sergey12malyshev/RF_HACK/application/workStates.c

#include <stdbool.h>

#include "workStates.h"

static Work_state_t mainState;

void setWorkState(const Work_state_t s)
{
  mainState = s;
}

Work_state_t getWorkState(void)
{
  return mainState;
}

bool isWorkStateSet(Work_state_t s)
{
  return (bool) (s == mainState);
}
