sergey12malyshev/RF_HACK/Core/Src/adc.c

/**
  ******************************************************************************
  * @file    adc.c
  * @brief   This file provides code for the configuration
  *          of the ADC instances.
  ******************************************************************************
  * @attention
  *
  * <h2><center>&copy; Copyright (c) 2024 STMicroelectronics.
  * All rights reserved.</center></h2>
  *
  * This software component is licensed by ST under BSD 3-Clause license,
  * the "License"; You may not use this file except in compliance with the
  * License. You may obtain a copy of the License at:
  *                        opensource.org/licenses/BSD-3-Clause
  *
  ******************************************************************************
  */

/* Includes ------------------------------------------------------------------*/
#include "adc.h"

/* USER CODE BEGIN 0 */

typedef struct _Adc
{
  uint16_t adc;
  uint32_t voltage;
  uint32_t voltage_average;
}Adc;

static Adc vdda = {0};

uint16_t getAdcVDDA(void)
{
  return vdda.adc;
}

uint32_t getVoltageVDDA(void)
{
  return vdda.voltage;
}

uint32_t getVoltageVDDA_Av(void)
{
  return vdda.voltage_average;
}

char generateRandomChar(void)
{
  return (char)(getAdcVDDA() & 127);
}

void adc_enable(void)
{
  __IO uint32_t wait_loop_index = 0;

  LL_ADC_Enable(ADC1);

  wait_loop_index = ((LL_ADC_DELAY_TEMPSENSOR_STAB_US * (SystemCoreClock / (100000 * 2))) / 10); //!!!
  while(wait_loop_index != 0)
  {
    wait_loop_index--;
  }
  // ADC calibration is not required for the stm32F4 series
}

static uint16_t adc_convertData(void)
{
  LL_ADC_REG_StartConversionSWStart(ADC1);
  while (!LL_ADC_IsActiveFlag_EOCS(ADC1)) {}
  LL_ADC_ClearFlag_EOCS(ADC1);

  return LL_ADC_REG_ReadConversionData12(ADC1);
}

static uint32_t adc_convertVDDA(uint16_t adcData)
{
  return (((uint32_t) *VREFINT_CAL_ADDR) * (uint32_t)3300) / adcData;
}

/* 
* Exponential running average  filt = (A * filt + signal) >> k, https://alexgyver.ru/lessons/filters/ 
*/
static uint32_t filt = 0;

uint16_t expRunningAverageFilter(uint16_t input)
{
  const uint8_t k = 2;
  const uint8_t a = 3; // a =  (2^k) – 1

  filt = (a * filt + input) >> k;

  return filt;
}

/*
* Preset the filter to speed up getting the correct value
*/
void setDefaultValueFilter(uint16_t defValue)
{
  filt = defValue;
}

void adcConvertProcess(void)
{
  vdda.adc = adc_convertData();
  vdda.voltage = adc_convertVDDA(vdda.adc);
  vdda.voltage_average = expRunningAverageFilter(vdda.voltage);
}


/* USER CODE END 0 */

/* ADC1 init function */
void MX_ADC1_Init(void)
{

  LL_ADC_InitTypeDef ADC_InitStruct = {0};
  LL_ADC_REG_InitTypeDef ADC_REG_InitStruct = {0};
  LL_ADC_CommonInitTypeDef ADC_CommonInitStruct = {0};

  /* Peripheral clock enable */
  LL_APB2_GRP1_EnableClock(LL_APB2_GRP1_PERIPH_ADC1);

  /** Common config
  */
  ADC_InitStruct.Resolution = LL_ADC_RESOLUTION_12B;
  ADC_InitStruct.DataAlignment = LL_ADC_DATA_ALIGN_RIGHT;
  ADC_InitStruct.SequencersScanMode = LL_ADC_SEQ_SCAN_DISABLE;
  LL_ADC_Init(ADC1, &ADC_InitStruct);
  ADC_REG_InitStruct.TriggerSource = LL_ADC_REG_TRIG_SOFTWARE;
  ADC_REG_InitStruct.SequencerLength = LL_ADC_REG_SEQ_SCAN_DISABLE;
  ADC_REG_InitStruct.SequencerDiscont = LL_ADC_REG_SEQ_DISCONT_DISABLE;
  ADC_REG_InitStruct.ContinuousMode = LL_ADC_REG_CONV_SINGLE;
  ADC_REG_InitStruct.DMATransfer = LL_ADC_REG_DMA_TRANSFER_NONE;
  LL_ADC_REG_Init(ADC1, &ADC_REG_InitStruct);
  LL_ADC_REG_SetFlagEndOfConversion(ADC1, LL_ADC_REG_FLAG_EOC_UNITARY_CONV);
  ADC_CommonInitStruct.CommonClock = LL_ADC_CLOCK_SYNC_PCLK_DIV4;
  LL_ADC_CommonInit(__LL_ADC_COMMON_INSTANCE(ADC1), &ADC_CommonInitStruct);
  /** Configure Regular Channel
  */
  LL_ADC_REG_SetSequencerRanks(ADC1, LL_ADC_REG_RANK_1, LL_ADC_CHANNEL_VREFINT);
  LL_ADC_SetChannelSamplingTime(ADC1, LL_ADC_CHANNEL_VREFINT, LL_ADC_SAMPLINGTIME_3CYCLES);
  LL_ADC_SetCommonPathInternalCh(__LL_ADC_COMMON_INSTANCE(ADC1), LL_ADC_PATH_INTERNAL_VREFINT);
}

/************************ (C) COPYRIGHT STMicroelectronics *****END OF FILE****/
