sergey12malyshev/RF_HACK/application/cli_Thread.h

#pragma once
#ifndef __CLI_TASK_H__
#define __CLI_TASK_H__

#define LC_INCLUDE "lc-addrlabels.h"
#include "pt.h"

PT_THREAD(CLI_Thread(struct pt *pt));

void cli_init(void);
void cli_uart_callBack(void);

#endif /*__CLI_TASK_H__ */
