sergey12malyshev/RF_HACK/application/configFile.h

#pragma once

#ifndef _CONFIG_H_
#define _CONFIG_H_

#include <stdbool.h>

#define CALIBRATE_EN              false       // Activating touchscreen calibration

#define RUN_LCD_DEMO              false       // Enabling demo mode for the display

#define CC1101_CUSTOM_OLD_CONFIG  false       // Enabling old CC1101 initialization

#define TX_MODE_ALWAYS            false       // Enabling continuous transmission mode

#define CLI_ENABLE                true        // Enabling the command line

#endif // _CONFIG_H_
