sergey12malyshev/RF_HACK/application/subGHz_TX_Thread.c

#include <stdbool.h>
#include <stdlib.h>
#include <stdio.h>
#include <string.h>

#define LC_INCLUDE "lc-addrlabels.h"
#include "pt.h"

#include "main.h"
#include "subGHz_TX_Thread.h"
#include "application_Thread.h"
#include "cli_driver.h"
#include "cc1101.h"
#include "time.h"

#include "display.h"
#include "displayInit.h"
#include "ili9341.h"


static char packet[7] = "QWERTY";; // Reserve one character for a null terminator!

/*
 * Protothread subGHz_TX_Thread
 *
 *
 */
PT_THREAD(subGHz_TX_Thread(struct pt *pt))
{
  static uint32_t timer1;
  
  PT_BEGIN(pt);

  PT_DELAY_MS(pt, &timer1, 250);
  
  screen_clear();
  LCD_WriteString(lcd, 0, 0, "TX mode", &Font_8x13, COLOR_RED, COLOR_BLACK, LCD_SYMBOL_PRINT_FAST);

  CC1101_reinit();

  setTime(&timer1);


  while (1)
  {       
    PT_WAIT_UNTIL(pt, timer(&timer1, 350));

    static uint8_t count_tx = 0;

    if (count_tx >= 99)
    {
      count_tx = 0;
    }
    sprintf(packet, "TST %02d", count_tx++);

    uint8_t result = CC1101_transmitt_packet(packet, sizeof(packet)); // the function is sending the data

    if (result > 0)
    {
      DEBUG_PRINT("TX ERROR: %d"CLI_NEW_LINE, result);
    }

    LCD_WriteString(lcd, 15, 40, packet, &Font_12x20, COLOR_RED, COLOR_BLACK, LCD_SYMBOL_PRINT_FAST);

    static uint32_t tx_timeout;
    tx_timeout = HAL_GetTick() + 100;

    PT_WAIT_UNTIL(pt, (CC1101_GDO0_flag_get() || (HAL_GetTick() > tx_timeout))); // (low lowel - end transmitt)
    if (!CC1101_GDO0_flag_get())
    {
      DEBUG_PRINT("TX TIMEOUT"CLI_NEW_LINE);
    }
    CC1101_GDO0_flag_clear();

    PT_YIELD(pt);
  }

  PT_END(pt);
}
