sergey12malyshev/RF_HACK/application/frequencyChannelsTable.c

#include "frequencyChannelsTable.h"

const float freqLpdList[69] = 
{
  LPD1, LPD2, LPD3, LPD4, LPD5, LPD6, LPD7, LPD8, LPD9, LPD10, LPD11, LPD12, LPD13, LPD14, LPD15, LPD16, LPD17, LPD18, LPD19,
  LPD20, LPD21, LPD22, LPD23, LPD24, LPD25, LPD26, LPD27, LPD28, LPD29, LPD30, LPD31, LPD32, LPD33, LPD34, LPD35, LPD36, LPD37, 
  LPD38, LPD39, LPD40, LPD41, LPD42, LPD43, LPD44, LPD45, LPD46, LPD47, LPD48, LPD49, LPD50, LPD51, LPD52, LPD53, LPD54, LPD55, 
  LPD56, LPD57, LPD58, LPD59, LPD60, LPD61, LPD62, LPD63, LPD64, LPD65, LPD66, LPD67, LPD68, LPD69
};
