sergey12malyshev/RF_HACK/application/frequencyChannelsTable.h

#pragma once

#define LPD1    433.075
#define LPD2    433.100
#define LPD3    433.125
#define LPD4    433.150
#define LPD5    433.175
#define LPD6    433.200
#define LPD7    433.225
#define LPD8    433.250
#define LPD9    433.275
#define LPD10   433.300
#define LPD11   433.325
#define LPD12   433.350
#define LPD13   433.375
#define LPD14   433.400
#define LPD15   433.425
#define LPD16   433.450
#define LPD17   433.475
#define LPD18   433.500
#define LPD19   433.525
#define LPD20   433.550
#define LPD21   433.575
#define LPD22   433.600
#define LPD23   433.625
#define LPD24   433.650
#define LPD25   433.675
#define LPD26   433.700
#define LPD27   433.725
#define LPD28   433.750
#define LPD29   433.775
#define LPD30   433.800
#define LPD31   433.825
#define LPD32   433.850
#define LPD33   433.875
#define LPD34   433.900
#define LPD35   433.925
#define LPD36   433.950
#define LPD37   433.975
#define LPD38   434.000
#define LPD39   434.025
#define LPD40   434.050
#define LPD41   434.075
#define LPD42   434.100
#define LPD43   434.125
#define LPD44   434.150
#define LPD45   434.175
#define LPD46   434.200
#define LPD47   434.225
#define LPD48   434.250
#define LPD49   434.275
#define LPD50   434.300
#define LPD51   434.325
#define LPD52   434.350
#define LPD53   434.375
#define LPD54   434.400
#define LPD55   434.425
#define LPD56   434.450
#define LPD57   434.475
#define LPD58   434.500
#define LPD59   434.525
#define LPD60   434.550
#define LPD61   434.575
#define LPD62   434.600
#define LPD63   434.625
#define LPD64   434.650
#define LPD65   434.675
#define LPD66   434.700
#define LPD67   434.725
#define LPD68   434.750
#define LPD69   434.775


#define PMR1	446.00625
#define PMR2	446.01875
#define PMR3	446.03125
#define PMR4	446.04375
#define PMR5	446.05625
#define PMR6	446.06875
#define PMR7	446.08125
#define PMR8	446.09375
#define PMR9	446.10625
#define PMR10	446.11875
#define PMR11	446.13125
#define PMR12	446.14375
#define PMR13	446.15625
#define PMR14	446.16875
#define PMR15	446.18125
#define PMR16	446.19375

extern const float freqLpdList[69];
